ReclaimerLabs/RGBMatrixPanelCPLD-PhotonBackpack/hardware/rgbmatrixpanel_cpld_DATA.C

/***************************************************************************************

	Lattice Semiconductor Corp.
	Slim VME Data File.

	CREATED BY:    ispVM System Version 18.1
	CREATION DATE: Wed Jun 08 00:33:04 2016

	CHAIN DESCRIPTION:
	1	LC4032V	Erase,Program,Verify	D:\Projects\RGBMatrixPanelCPLD-PhotonBackpack\hardware\rgbmatrixpanel_cpld.jed

	The following constant variables should be stored in external data.

***************************************************************************************/

xdata const int g_iDataSize = 2315;
xdata const unsigned char g_pucDataArray[ 2315 ] = {
0x00, 0xFF, 0xF4, 0x21, 0x08, 0x63, 0x14, 0xE4, 0x3F, 0x0F, 0xFF, 0xFF, 0xFF, 0x9F, 0x67, 
0xE1, 0xF8, 0x7E, 0x1F, 0xFC, 0x3F, 0xFF, 0xFF, 0xA2, 0xDB, 0xD4, 0x21, 0x08, 0x23, 0x10, 
0xC4, 0x3F, 0x0F, 0xFF, 0xFF, 0x7D, 0x1F, 0xA7, 0xD1, 0xF8, 0x7E, 0x1F, 0xFC, 0x3F, 0xFF, 
0xFF, 0xA2, 0xFF, 0xF4, 0x21, 0x08, 0x63, 0x14, 0xE4, 0x3F, 0x0F, 0xFF, 0xFF, 0xFF, 0x9F, 
0x87, 0xF1, 0xF8, 0x7E, 0x1F, 0xFC, 0x3F, 0xFF, 0xFF, 0xA2, 0xDB, 0xD4, 0x21, 0x08, 0x23, 
0x10, 0xC4, 0x3F, 0x0F, 0xFF, 0xFF, 0x7D, 0x1F, 0x67, 0xF1, 0xF8, 0x7E, 0x1F, 0xFC, 0x3F, 
0xFF, 0xFF, 0xA2, 0xFF, 0xF4, 0x21, 0x08, 0x63, 0x14, 0xE0, 0x3F, 0x0F, 0xFF, 0xFF, 0xFF, 
0x9F, 0xE7, 0xF1, 0xF8, 0x7E, 0x1F, 0xFC, 0x3F, 0xFF, 0xFF, 0xA2, 0xDF, 0xF4, 0x21, 0x08, 
0x63, 0x14, 0xE4, 0x3F, 0x0F, 0xFF, 0xFF, 0xFF, 0x9F, 0xE7, 0xF1, 0xF8, 0x7E, 0x1F, 0xFC, 
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
0xFF, 0xFF, 0xFF, 0xFF, 0xFF, 0xFF, 0xFF, 0xFF, 0xFF, 0xFF, 0xFF, 0xFF, 0xFF, 0xFF, 0xFF, 
0xFF, 0xFF, 0xFF, 0xFF, 0xFF, 0xA2, 0xFF, 0xFF, 0xFF, 0xFF, 0xFF, 0xFF, 0xFF, 0xFF, 0xFF, 
0xFF, 0xFF, 0xFF, 0xFF, 0xFF, 0xFF, 0xFF, 0xFF, 0xFF, 0xFF, 0xFF, 0xFF, 0xFF, 0xA2, 0xFF, 
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
