ReclaimerLabs/RGBMatrixPanelCPLD-PhotonBackpack/hardware/rgbmatrixpanel_cpld_ALGO.C

/***************************************************************************************

	Lattice Semiconductor Corp.
	Slim VME Algo File.

	CREATED BY:    ispVM System Version 18.1
	CREATION DATE: Wed Jun 08 00:33:04 2016

	CHAIN DESCRIPTION:
	1	LC4032V	Erase,Program,Verify	D:\Projects\RGBMatrixPanelCPLD-PhotonBackpack\hardware\rgbmatrixpanel_cpld.jed

	The following constant variables should be stored in external data.

***************************************************************************************/

xdata const int g_iAlgoSize = 284;
xdata const unsigned char g_pucAlgoArray[ 284 ] = {
0x5F, 0x53, 0x56, 0x4D, 0x45, 0x31, 0x2E, 0x33, 0x08, 0x00, 0x06, 0x00, 0x09, 0x00, 0x07, 
0x00, 0x02, 0x03, 0x03, 0x02, 0x10, 0x01, 0x11, 0x08, 0x13, 0x68, 0x70, 0x10, 0x01, 0x12, 
0x20, 0x13, 0xFF, 0xFF, 0xFF, 0xFF, 0x14, 0xC2, 0x0A, 0x01, 0x80, 0x15, 0xFF, 0xFF, 0xFF, 
0xF0, 0x70, 0x11, 0x08, 0x13, 0x38, 0x70, 0x12, 0x44, 0x13, 0x00, 0x00, 0x00, 0x00, 0x00, 
0x00, 0x00, 0x00, 0x00, 0x70, 0x11, 0x08, 0x13, 0xA8, 0x70, 0x10, 0x01, 0x1B, 0x03, 0x1A, 
0x14, 0x11, 0x08, 0x13, 0xC0, 0x70, 0x10, 0x01, 0x1B, 0x03, 0x1A, 0x64, 0x11, 0x08, 0x13, 
0x28, 0x70, 0x10, 0x01, 0x1B, 0x03, 0x1A, 0x0A, 0x11, 0x08, 0x13, 0x84, 0x70, 0x10, 0x01, 
0x11, 0x08, 0x13, 0xE4, 0x70, 0xA0, 0x64, 0xA4, 0x12, 0xAC, 0x01, 0xA6, 0xA3, 0x70, 0x10, 
0x01, 0x1B, 0x03, 0x1A, 0x0D, 0xA1, 0x11, 0x08, 0x13, 0x80, 0x70, 0x12, 0x64, 0xA6, 0xA3, 
0x70, 0x11, 0x08, 0x13, 0x54, 0x70, 0xA0, 0x64, 0xA5, 0x10, 0x01, 0x1B, 0x03, 0x1A, 0x01, 
0x12, 0xAC, 0x01, 0x13, 0x00, 0x00, 0x00, 0x00, 0x00, 0x00, 0x00, 0x00, 0x00, 0x00, 0x00, 
0x00, 0x00, 0x00, 0x00, 0x00, 0x00, 0x00, 0x00, 0x00, 0x00, 0x00, 0xA7, 0xA3, 0x70, 0xA1, 
0x11, 0x08, 0x13, 0x58, 0x70, 0x12, 0x20, 0x13, 0xFF, 0xFF, 0xFF, 0xFF, 0x70, 0x10, 0x01, 
0x1B, 0x03, 0x1A, 0x0D, 0x11, 0x08, 0x13, 0xE8, 0x70, 0x12, 0x20, 0x13, 0xFF, 0xFF, 0xFF, 
0xFF, 0x14, 0xFF, 0xFF, 0xFF, 0xFF, 0x70, 0x11, 0x08, 0x13, 0xF4, 0x70, 0x10, 0x01, 0x1B, 
0x05, 0x1A, 0x32, 0x11, 0x08, 0x13, 0xF4, 0x70, 0x10, 0x01, 0x1B, 0x05, 0x1A, 0x32, 0x11, 
0x08, 0x13, 0x78, 0x70, 0x10, 0x01, 0x1B, 0x05, 0x1A, 0xC8, 0x01, 0x11, 0x08, 0x13, 0xFF, 
0x70, 0x10, 0x01, 0x1B, 0x20, 0x1A, 0x0A, 0x11, 0x08, 0x13, 0x68, 0x14, 0xB8, 0x15, 0xFF, 
0x70, 0x11, 0x08, 0x13, 0x78, 0x70, 0x10, 0x01, 0x1B, 0x03, 0x1A, 0xC8, 0x01, 0x7F };
